nstielau/digirdu-lights/tests/test_sound_review.py

"""Tests for offline review through the producer audio pipeline."""

import array
import hashlib
import json
import math
import os
from pathlib import Path
import subprocess
import sys
import tempfile
import unittest
from unittest.mock import patch
import wave

from audio_features import Analyzer, AudioFeatures
from audio_events import DroneEventConfig
from animation import CulvertAnimation
from config import Config
from effects import FEATHERWING_PORTRAIT
from tools import sound_review
from tools.sound_review import (
    analyze_wav,
    build_artifacts,
    compare_drone,
    compare_labels,
    load_labels,
    portrait_pixels,
    read_wav_hops,
    render_effects,
    serialize_features,
)
from tools.record_fixture import validate_wav as validate_fixture_wav


FIXTURE_DIR = Path(__file__).parent.parent / "review" / "recordings"
REVIEW_AUDIO_FIXTURE = FIXTURE_DIR / "drone-yell-10s.wav"
REVIEW_LABEL_FIXTURE = FIXTURE_DIR / "drone-yell-10s.labels.json"
HIGH_YELL_AUDIO_FIXTURE = FIXTURE_DIR / "high-yell-01.wav"
HIGH_YELL_LABEL_FIXTURE = FIXTURE_DIR / "high-yell-01.labels.json"
REVIEW_AUDIO_SHA256 = "efa8b234ee94c014437b7d48fd6f612cd8aed68bb49764d009c5cb97f7cfafa2"


def write_pcm_wav(path, sample_rate_hz, samples):
    path = Path(path)
    little_endian = array.array("h", samples)
    if sys.byteorder != "little":
        little_endian.byteswap()
    with wave.open(str(path), "wb") as destination:
        destination.setnchannels(1)
        destination.setsampwidth(2)
        destination.setframerate(sample_rate_hz)
        destination.writeframes(little_endian.tobytes())
    return path


def fixture_feature_frames():
    """Small serialized feature timeline for deterministic renderer tests."""
    frames = []
    for time_ms in range(0, 1001, 100):
        level = 0.2 if time_ms < 500 else 0.8
        frames.append(
            {
                "time_ms": time_ms,
                "calibrating": False,
                "volume": level,
                "drone": level,
                "harmonics": 0.35,
                "timbre_position": 0.25,
                "growl": 0.15,
                "vocal": 0.1,
                "transient_strength": 0.0,
                "attack_event": False,
                "yell_event": False,
                "attack_age_s": 0.0,
                "yell_age_s": 0.0,
                "decay": level,
                "low_energy": 0.55,
                "mid_energy": 0.3,
                "high_energy": 0.15,
                "spectrum": (level, 0.5, 0.25, 0.1, 0.05, 0.0, 0.0, 0.0),
                "active": level > 0.0,
                "raw_rms": 100.0,
                "dominant_frequency_hz": 93.75,
            }
        )
    return frames


class CommittedSoundReviewFixtureTests(unittest.TestCase):
    def test_committed_fixture_is_reviewed_and_deterministic(self):
        self.assertEqual(
            hashlib.sha256(REVIEW_AUDIO_FIXTURE.read_bytes()).hexdigest(),
            REVIEW_AUDIO_SHA256,
        )
        self.assertEqual(
            validate_fixture_wav(REVIEW_AUDIO_FIXTURE),
            {
                "sample_rate_hz": 16000,
                "channels": 1,
                "sample_width_bytes": 2,
                "frame_count": 160000,
                "duration_s": 10.0,
            },
        )
        expected_labels = {
            "audio_file": REVIEW_AUDIO_FIXTURE.name,
            "sample_rate_hz": 16000,
            "labels": [
                {"type": "drone", "start_ms": 2250, "end_ms": 10000},
                {"type": "yell", "start_ms": 4250, "end_ms": 4750},
            ],
        }
        self.assertEqual(json.loads(REVIEW_LABEL_FIXTURE.read_text()), expected_labels)
        label_bytes = REVIEW_LABEL_FIXTURE.read_bytes()

        with tempfile.TemporaryDirectory() as temporary:
            temporary = Path(temporary)
            first = build_artifacts(
                REVIEW_AUDIO_FIXTURE, REVIEW_LABEL_FIXTURE, temporary / "first"
            )
            second = build_artifacts(
                REVIEW_AUDIO_FIXTURE, REVIEW_LABEL_FIXTURE, temporary / "second"
            )

            self.assertEqual(REVIEW_LABEL_FIXTURE.read_bytes(), label_bytes)
            first_events = json.loads(Path(first["events_json"]).read_text())
            event_times = [event["time_ms"] for event in first_events]
            self.assertEqual(event_times, sorted(event_times))
            self.assertTrue(all(0 <= time_ms <= 10000 for time_ms in event_times))
            for name in first:
                self.assertEqual(
                    Path(first[name]).read_bytes(),
                    Path(second[name]).read_bytes(),
                    name,
                )

    def test_high_yell_recording_has_authoritative_human_labels(self):
        self.assertEqual(
            validate_fixture_wav(HIGH_YELL_AUDIO_FIXTURE),
            {
                "sample_rate_hz": 16000,
                "channels": 1,
                "sample_width_bytes": 2,
                "frame_count": 160000,
                "duration_s": 10.0,
            },
        )
        self.assertEqual(
            json.loads(HIGH_YELL_LABEL_FIXTURE.read_text()),
            {
                "audio_file": "high-yell-01.wav",
                "sample_rate_hz": 16000,
                "labels": [
                    {"type": "drone", "start_ms": 1020, "end_ms": 6950},
                    {"type": "yell", "start_ms": 2950, "end_ms": 3050},
                ],
            },
        )


class SoundReviewWavTests(unittest.TestCase):
    def setUp(self):
        self.temporary = tempfile.TemporaryDirectory()
        self.addCleanup(self.temporary.cleanup)
        self.tempdir = Path(self.temporary.name)

    def test_read_wav_hops_uses_complete_1024_sample_frames(self):
        path = write_pcm_wav(
            self.tempdir / "take.wav", 16000, array.array("h", range(2048))
        )

        info, hops = read_wav_hops(path, Config())

        self.assertEqual(info["sample_rate_hz"], 16000)
        self.assertEqual([len(hop) for hop in hops], [1024, 1024])
        self.assertEqual(hops[0], array.array("h", range(1024)))
        self.assertEqual(hops[1], array.array("h", range(1024, 2048)))

    def test_exact_10_second_wav_pads_only_final_analysis_hop_and_builds_review(self):
        config = Config()
        sample_count = 10 * config.sample_rate
        samples = array.array("h", [0]) * sample_count
        samples[-256:] = array.array("h", range(1, 257))
        path = write_pcm_wav(self.tempdir / "take.wav", config.sample_rate, samples)
        labels_path = self.tempdir / "take.labels.json"
        labels_path.write_text(
            json.dumps(
                {
                    "audio_file": path.name,
                    "sample_rate_hz": config.sample_rate,
                    "labels": [],
                }
            )
        )

        info, hops = read_wav_hops(path, config)

        self.assertEqual(info["frame_count"], 160000)
        self.assertEqual(info["duration_ms"], 10000)
        self.assertEqual(len(hops), 157)
        self.assertEqual(len(hops[-1]), config.hop_size)
        self.assertEqual(hops[-1][:256], array.array("h", range(1, 257)))
        self.assertEqual(hops[-1][256:], array.array("h", [0]) * 768)

        seen_dts = []
        original_update = Analyzer.update

        def record_update(analyzer, raw, dt_s):
            seen_dts.append(dt_s)
            return original_update(analyzer, raw, dt_s)

        with patch.object(Analyzer, "update", record_update):
            artifacts = build_artifacts(
                path, labels_path, self.tempdir / "artifacts", config
            )
        result = json.loads(Path(artifacts["run_json"]).read_text())
        features = json.loads(Path(artifacts["features_json"]).read_text())
        bundle = json.loads(Path(artifacts["review_json"]).read_text())

        self.assertEqual(result["duration_ms"], 10000)
        self.assertEqual(len(seen_dts), 157)
        self.assertEqual(seen_dts[0], config.hop_size / config.sample_rate)
        self.assertEqual(seen_dts[-1], 0.016)
        self.assertEqual(features[-1]["time_ms"], 10000)
        self.assertNotIn(10048, [frame["time_ms"] for frame in features])
        self.assertEqual(bundle["duration_ms"], 10000)
        self.assertEqual(bundle["audio_url"], "../take.wav")
        self.assertEqual(bundle["features"], features)

    def test_read_wav_hops_rejects_invalid_wav_format(self):
        path = write_pcm_wav(
            self.tempdir / "take.wav", 8000, array.array("h", range(1024))
        )

        with self.assertRaises(ValueError):
            read_wav_hops(path, Config())

    def test_read_wav_hops_rejects_file_replacement_during_validation(self):
        path = write_pcm_wav(
            self.tempdir / "take.wav", 16000, array.array("h", range(2048))
        )
        replacement = write_pcm_wav(
            self.tempdir / "replacement.wav",
            16000,
            array.array("h", [42]) * 2048,
        )

        def validate_then_replace(*args, **kwargs):
            metadata = validate_fixture_wav(*args, **kwargs)
            os.replace(replacement, path)
            return metadata

        with patch(
            "tools.sound_review.validate_wav", side_effect=validate_then_replace
        ):
            with self.assertRaisesRegex(ValueError, "changed during validation"):
                read_wav_hops(path, Config())

    def test_read_wav_hops_rejects_metadata_changes_during_validation(self):
        path = write_pcm_wav(
            self.tempdir / "take.wav", 16000, array.array("h", range(2048))
        )

        def validate_with_stale_metadata(*args, **kwargs):
            metadata = dict(validate_fixture_wav(*args, **kwargs))
            metadata["frame_count"] = 1024
            return metadata

        with patch(
            "tools.sound_review.validate_wav",
            side_effect=validate_with_stale_metadata,
        ):
            with self.assertRaisesRegex(ValueError, "metadata changed"):
                read_wav_hops(path, Config())

    def test_load_labels_rejects_invalid_range_and_wrong_rate(self):
        path = self.tempdir / "labels.json"
        path.write_text(
            json.dumps(
                {
                    "audio_file": "take.wav",
                    "sample_rate_hz": 8000,
                    "labels": [
                        {"type": "drone", "start_ms": 900, "end_ms": 100}
                    ],
                }
            )
        )

        with self.assertRaises(ValueError):
            load_labels(path, duration_ms=1000, sample_rate_hz=16000)

    def test_load_labels_rejects_invalid_types_and_timestamps(self):
        invalid_labels = (
            {"type": "unknown", "start_ms": 100, "end_ms": 200},
            {"type": [], "start_ms": 100, "end_ms": 200},
            {"type": "drone", "start_ms": 100.5, "end_ms": 200},
            {"type": "drone", "start_ms": True, "end_ms": 200},
            {"type": "drone", "start_ms": -1, "end_ms": 200},
            {"type": "drone", "start_ms": 200, "end_ms": 100},
            {"type": "drone", "start_ms": 100, "end_ms": 1001},
        )
        for label in invalid_labels:
            with self.subTest(label=label):
                path = self.tempdir / "labels.json"
                path.write_text(
                    json.dumps(
                        {
                            "audio_file": "take.wav",
                            "sample_rate_hz": 16000,
                            "labels": [label],
                        }
                    )
                )
                with self.assertRaises(ValueError):
                    load_labels(path, duration_ms=1000, sample_rate_hz=16000)

    def test_load_labels_enforces_range_and_point_grammar(self):
        invalid_labels = (
            {"type": "drone", "start_ms": 100},
            {"type": "yell", "start_ms": 100, "end_ms": 100},
            {"type": "beat", "start_ms": 100, "end_ms": 101},
            {"type": "transient", "start_ms": 100, "end_ms": 200},
        )
        for index, label in enumerate(invalid_labels):
            with self.subTest(label=label):
                path = self.tempdir / f"invalid-grammar-{index}.json"
                path.write_text(
                    json.dumps(
                        {
                            "audio_file": "take.wav",
                            "sample_rate_hz": 16000,
                            "labels": [label],
                        }
                    )
                )
                with self.assertRaises(ValueError):
                    load_labels(path, duration_ms=1000, sample_rate_hz=16000)

        path = self.tempdir / "valid-points.json"
        path.write_text(
            json.dumps(
                {
                    "audio_file": "take.wav",
                    "sample_rate_hz": 16000,
                    "labels": [
                        {"type": "beat", "start_ms": 100},
                        {"type": "transient", "start_ms": 200, "end_ms": 200},
                    ],
                }
            )
        )
        self.assertEqual(
            load_labels(path, duration_ms=1000, sample_rate_hz=16000)["labels"],
            [
                {"type": "beat", "start_ms": 100, "end_ms": 100},
                {"type": "transient", "start_ms": 200, "end_ms": 200},
            ],
        )

    def test_load_labels_accepts_growl_range(self):
        path = self.tempdir / "growl-labels.json"
        path.write_text(
            json.dumps(
                {
                    "audio_file": "take.wav",
                    "sample_rate_hz": 16000,
                    "labels": [
                        {"type": "growl", "start_ms": 2500, "end_ms": 4500}
                    ],
                }
            )
        )
        self.assertEqual(
            load_labels(path, duration_ms=10000, sample_rate_hz=16000)["labels"],
            [{"type": "growl", "start_ms": 2500, "end_ms": 4500}],
        )

    def test_load_labels_rejects_invalid_document_shapes(self):
        invalid_documents = (
            [],
            {"sample_rate_hz": 16000, "labels": []},
            {"audio_file": "", "sample_rate_hz": 16000, "labels": []},
            {"audio_file": "take.wav", "sample_rate_hz": True, "labels": []},
            {"audio_file": "take.wav", "sample_rate_hz": 16000, "labels": {}},
            {
                "audio_file": "take.wav",
                "sample_rate_hz": 16000,
                "labels": ["drone"],
            },
        )
        for index, document in enumerate(invalid_documents):
            with self.subTest(document=document):
                path = self.tempdir / f"labels-{index}.json"
                path.write_text(json.dumps(document))
                with self.assertRaises(ValueError):
                    load_labels(path, duration_ms=1000, sample_rate_hz=16000)

    def test_load_labels_rejects_duplicate_metadata(self):
        path = self.tempdir / "labels.json"
        path.write_text(
            '{"audio_file":"first.wav","audio_file":"second.wav",'
            '"sample_rate_hz":16000,"labels":[]}'
        )

        with self.assertRaises(ValueError):
            load_labels(path, duration_ms=1000, sample_rate_hz=16000)


class SoundReviewAnalysisTests(unittest.TestCase):
    def setUp(self):
        self.temporary = tempfile.TemporaryDirectory()
        self.addCleanup(self.temporary.cleanup)
        self.tempdir = Path(self.temporary.name)

    def test_spectrogram_preview_maps_silence_to_fixed_floor(self):
        config = Config()
        hops = [array.array("h", [0]) * config.hop_size for _ in range(2)]

        self.assertTrue(hasattr(sound_review, "spectrogram_preview"))
        preview = sound_review.spectrogram_preview(hops, config)

        self.assertEqual(preview["min_frequency_hz"], 31.25)
        self.assertEqual(preview["max_frequency_hz"], 8000.0)
        self.assertEqual(preview["min_dbfs"], -90.0)
        self.assertEqual(preview["max_dbfs"], 0.0)
        self.assertEqual(preview["rows"], 64)
        self.assertEqual(preview["columns"], 2)
        self.assertEqual(preview["frames"], [[0] * 64, [0] * 64])

    def test_spectrogram_preview_places_tone_in_expected_log_band(self):
        config = Config()
        frequency_hz = 500.0
        samples = array.array(
            "h",
            (
                round(
                    12000
                    * math.sin(
                        2
                        * math.pi
                        * frequency_hz
                        * index
                        / config.sample_rate
                    )
                )
                for index in range(config.hop_size)
            ),
        )

        self.assertTrue(hasattr(sound_review, "spectrogram_preview"))
        first = sound_review.spectrogram_preview([samples], config)
        second = sound_review.spectrogram_preview([samples], config)
        peak_row = max(
            range(first["rows"]), key=first["frames"][0].__getitem__
        )
        expected_row = math.floor(
            math.log(frequency_hz / first["min_frequency_hz"])
            / math.log(
                first["max_frequency_hz"] / first["min_frequency_hz"]
            )
            * first["rows"]
        )

        self.assertEqual(first, second)
        self.assertLessEqual(abs(peak_row - expected_row), 1)
        self.assertGreater(first["frames"][0][peak_row], 0)
        self.assertTrue(
            all(0 <= value <= 255 for value in first["frames"][0])
        )

    def test_analyze_wav_uses_ordered_hop_end_timestamps_and_events(self):
        config = Config()
        frame_count = 10 * config.sample_rate // config.hop_size * config.hop_size
        samples = array.array("h")
        for index in range(frame_count):
            time_s = index / config.sample_rate
            value = 0.0
            if time_s >= 2.0:
                value += 3500 * math.sin(2 * math.pi * 93.75 * time_s)
            if 4.8 <= time_s < 5.2:
                value += 7000 * math.sin(2 * math.pi * 2500 * time_s)
            samples.append(round(value))
        audio_path = write_pcm_wav(
            self.tempdir / "take.wav", config.sample_rate, samples
        )
        duration_ms = round(frame_count * 1000 / config.sample_rate)
        labels_path = self.tempdir / "labels.json"
        labels_path.write_text(
            json.dumps(
                {
                    "audio_file": audio_path.name,
                    "sample_rate_hz": config.sample_rate,
                    "labels": [
                        {"type": "drone", "start_ms": 2000, "end_ms": duration_ms},
                        {"type": "yell", "start_ms": 4800, "end_ms": 5200},
                    ],
                }
            )
        )

        result = analyze_wav(audio_path, labels_path, config, fps=20)

        self.assertEqual(
            [frame["time_ms"] for frame in result["features"]],
            [
                round(index * config.hop_size * 1000 / config.sample_rate)
                for index in range(1, frame_count // config.hop_size + 1)
            ],
        )
        self.assertIn(
            result["events"][0]["type"], {"drone_start", "transient", "yell"}
        )
        self.assertEqual(result["fps"], 20)

    def test_analyze_wav_uses_exact_sample_end_delta_for_1025_samples(self):
        config = Config()
        audio_path = write_pcm_wav(
            self.tempdir / "unaligned.wav",
            config.sample_rate,
            array.array("h", [0]) * 1025,
        )
        labels_path = self.tempdir / "labels.json"
        labels_path.write_text(
            json.dumps(
                {
                    "audio_file": audio_path.name,
                    "sample_rate_hz": config.sample_rate,
                    "labels": [],
                }
            )
        )
        seen_dts = []
        original_update = Analyzer.update

        def record_update(analyzer, raw, dt_s):
            seen_dts.append(dt_s)
            return original_update(analyzer, raw, dt_s)

        with patch.object(Analyzer, "update", record_update):
            result = analyze_wav(audio_path, labels_path, config)

        timestamps = [frame["time_ms"] for frame in result["features"]]
        self.assertEqual(result["info"]["duration_ms"], 65)
        self.assertEqual(timestamps, [64, 65])
        self.assertEqual(seen_dts, [1024 / config.sample_rate, 1 / config.sample_rate])
        self.assertEqual(timestamps, sorted(set(timestamps)))

    def test_analyze_wav_uses_actual_duration_for_shorter_than_hop_audio(self):
        config = Config()
        audio_path = write_pcm_wav(
            self.tempdir / "short.wav",
            config.sample_rate,
            array.array("h", [0]) * 512,
        )
        labels_path = self.tempdir / "labels.json"
        labels_path.write_text(
            json.dumps(
                {
                    "audio_file": audio_path.name,
                    "sample_rate_hz": config.sample_rate,
                    "labels": [],
                }
            )
        )
        seen_dts = []
        original_update = Analyzer.update

        def record_update(analyzer, raw, dt_s):
            seen_dts.append(dt_s)
            return original_update(analyzer, raw, dt_s)

        with patch.object(Analyzer, "update", record_update):
            result = analyze_wav(audio_path, labels_path, config)

        self.assertEqual(result["info"]["duration_ms"], 32)
        self.assertEqual([frame["time_ms"] for frame in result["features"]], [32])
        self.assertEqual(seen_dts, [512 / config.sample_rate])

    def test_analyze_wav_rejects_labels_for_a_different_audio_file(self):
        config = Config()
        audio_path = write_pcm_wav(
            self.tempdir / "take.wav",
            config.sample_rate,
            array.array("h", [0]) * config.hop_size,
        )
        labels_path = self.tempdir / "labels.json"
        labels_path.write_text(
            json.dumps(
                {
                    "audio_file": "other.wav",
                    "sample_rate_hz": config.sample_rate,
                    "labels": [],
                }
            )
        )

        with self.assertRaises(ValueError):
            analyze_wav(audio_path, labels_path, config)

    def test_analyze_wav_rejects_invalid_fps(self):
        config = Config()
        audio_path = write_pcm_wav(
            self.tempdir / "take.wav",
            config.sample_rate,
            array.array("h", [0]) * config.hop_size,
        )
        labels_path = self.tempdir / "labels.json"
        labels_path.write_text(
            json.dumps(
                {
                    "audio_file": audio_path.name,
                    "sample_rate_hz": config.sample_rate,
                    "labels": [],
                }
            )
        )

        for fps in (True, 0, -1, math.nan, math.inf, -math.inf):
            with self.subTest(fps=fps):
                with self.assertRaises(ValueError):
                    analyze_wav(audio_path, labels_path, config, fps=fps)

    def test_serialize_features_is_normalized_finite_and_non_mutating(self):
        current = AudioFeatures()
        current.volume = 0.4
        current.drone = 0.5
        current.harmonics = 0.35
        current.timbrePosition = 0.25
        current.growl = 0.6
        current.vocal = 0.7
        current.attack = 0.8
        current.attackEvent = True
        current.yellEvent = False
        current.attackAge = 0.02
        current.yellAge = 0.0
        current.decay = 0.9
        current.spectrum = tuple(index / 10 for index in range(8))
        before = dict(vars(current))
        raw = {
            "rms": 123.0,
            "drone_hz": 93.75,
            "bands": (5.0, 3.0, 1.0, 0.5, 0.5),
        }

        serialized = serialize_features(current, raw, 64)

        self.assertEqual(vars(current), before)
        self.assertEqual(
            set(serialized),
            {
                "time_ms",
                "calibrating",
                "volume",
                "drone",
                "harmonics",
                "timbre_position",
                "growl",
                "vocal",
                "transient_strength",
                "attack_event",
                "yell_event",
                "attack_age_s",
                "yell_age_s",
                "decay",
                "low_energy",
                "mid_energy",
                "high_energy",
                "spectrum",
                "active",
                "raw_rms",
                "dominant_frequency_hz",
            },
        )
        for name in (
            "volume",
            "drone",
            "growl",
            "vocal",
            "transient_strength",
            "low_energy",
            "mid_energy",
            "high_energy",
        ):
            self.assertGreaterEqual(serialized[name], 0.0)
            self.assertLessEqual(serialized[name], 1.0)
        self.assertEqual(serialized["low_energy"], 0.5)
        self.assertEqual(serialized["mid_energy"], 0.4)
        self.assertEqual(serialized["high_energy"], 0.1)
        self.assertEqual(serialized["harmonics"], 0.35)
        self.assertEqual(serialized["timbre_position"], 0.25)
        self.assertTrue(serialized["attack_event"])
        self.assertFalse(serialized["yell_event"])
        self.assertEqual(serialized["attack_age_s"], 0.02)
        self.assertEqual(serialized["yell_age_s"], 0.0)
        self.assertEqual(serialized["decay"], 0.9)
        self.assertEqual(
            serialized["spectrum"], tuple(index / 10 for index in range(8))
        )

    def test_serialize_features_rejects_non_finite_values(self):
        current = AudioFeatures()
        raw = {
            "rms": math.inf,
            "drone_hz": 93.75,
            "bands": (0.0, 0.0, 0.0, 0.0, 0.0),
        }

        with self.assertRaises(ValueError):
            serialize_features(current, raw, 64)


class SoundReviewMetricTests(unittest.TestCase):
    def setUp(self):
        self.temporary = tempfile.TemporaryDirectory()
        self.addCleanup(self.temporary.cleanup)
        self.tempdir = Path(self.temporary.name)

    def test_compare_events_reports_one_match_one_false_positive_and_one_miss(self):
        labels = [
            {"type": "yell", "start_ms": 1000, "end_ms": 1200},
            {"type": "yell", "start_ms": 3000, "end_ms": 3200},
        ]
        detected = [
            {"type": "yell", "time_ms": 1100, "confidence": 0.9},
            {"type": "yell", "time_ms": 5000, "confidence": 0.7},
        ]

        report = compare_labels(labels, detected, tolerance_ms=250)

        self.assertEqual(report["yell"]["true_positive"], 1)
        self.assertEqual(report["yell"]["false_positive"], 1)
        self.assertEqual(report["yell"]["false_negative"], 1)
        self.assertAlmostEqual(report["yell"]["precision"], 0.5)
        self.assertAlmostEqual(report["yell"]["recall"], 0.5)
        self.assertAlmostEqual(report["yell"]["f1"], 0.5)
        self.assertEqual(report["yell"]["timing_error_ms"], [100])
        self.assertEqual(report["yell"]["absolute_timing_error_ms"], [100])

    def test_compare_labels_matches_each_detection_only_once(self):
        labels = [
            {"type": "beat", "start_ms": 1000, "end_ms": 1000},
            {"type": "beat", "start_ms": 2000, "end_ms": 2000},
        ]
        detected = [
            {"type": "beat", "time_ms": 1050},
            {"type": "beat", "time_ms": 2050},
            {"type": "beat", "time_ms": 2100},
        ]

        report = compare_labels(labels, detected, tolerance_ms=100)

        self.assertEqual(report["beat"]["true_positive"], 2)
        self.assertEqual(report["beat"]["false_positive"], 1)
        self.assertEqual(report["beat"]["false_negative"], 0)
        self.assertEqual(report["beat"]["unmatched_labels"], [])
        self.assertEqual(report["beat"]["unmatched_events"], [{"type": "beat", "time_ms": 2100}])

    def test_compare_labels_maximizes_matches_for_overlapping_ranges(self):
        labels = [
            {"type": "yell", "start_ms": 1000, "end_ms": 3000},
            {"type": "yell", "start_ms": 2000, "end_ms": 2050},
        ]
        detected = [
            {"type": "yell", "time_ms": 1800},
            {"type": "yell", "time_ms": 2500},
        ]

        report = compare_labels(labels, detected, tolerance_ms=250)

        self.assertEqual(report["yell"]["true_positive"], 2)
        self.assertEqual(report["yell"]["false_positive"], 0)
        self.assertEqual(report["yell"]["false_negative"], 0)
        self.assertEqual(report["yell"]["timing_error_ms"], [1500, -200])

    def test_compare_drone_reports_bounds_and_time_errors(self):
        report = compare_drone(
            {"start_ms": 2000, "end_ms": 8000},
            [
                {"type": "drone_start", "time_ms": 2200},
                {"type": "drone_stop", "time_ms": 7600},
            ],
            duration_ms=10000,
        )

        self.assertEqual(report["start_error_ms"], 200)
        self.assertEqual(report["stop_error_ms"], -400)
        self.assertAlmostEqual(report["intersection_over_union"], 5400 / 6000)
        self.assertEqual(report["false_active_ms"], 0)
        self.assertEqual(report["false_inactive_ms"], 600)

    def test_compare_drone_scores_disjoint_detected_spans_as_a_union(self):
        report = compare_drone(
            {"start_ms": 2000, "end_ms": 8000},
            [
                {"type": "drone_start", "time_ms": 1000},
                {"type": "drone_stop", "time_ms": 3000},
                {"type": "drone_start", "time_ms": 5000},
                {"type": "drone_stop", "time_ms": 6000},
            ],
            duration_ms=10000,
        )

        self.assertEqual(report["start_error_ms"], -1000)
        self.assertEqual(report["stop_error_ms"], -2000)
        self.assertAlmostEqual(report["intersection_over_union"], 2 / 7)
        self.assertEqual(report["false_active_ms"], 1000)
        self.assertEqual(report["false_inactive_ms"], 4000)

    def test_compare_drone_accepts_repeated_human_spans_without_changing_report_shape(self):
        report = compare_drone(
            [
                {"start_ms": 1000, "end_ms": 2000},
                {"start_ms": 4000, "end_ms": 5000},
            ],
            [
                {"type": "drone_start", "time_ms": 1000},
                {"type": "drone_stop", "time_ms": 2000},
                {"type": "drone_start", "time_ms": 4000},
                {"type": "drone_stop", "time_ms": 5000},
            ],
            duration_ms=10000,
        )

        self.assertEqual(
            set(report),
            {
                "start_error_ms",
                "stop_error_ms",
                "intersection_over_union",
                "false_active_ms",
                "false_inactive_ms",
            },
        )
        self.assertEqual(report["intersection_over_union"], 1.0)
        self.assertEqual(report["false_active_ms"], 0)
        self.assertEqual(report["false_inactive_ms"], 0)

    def test_compare_drone_reports_missing_bounds_without_dividing_by_zero(self):
        label = {"start_ms": 2000, "end_ms": 8000}

        for events, expected_start, expected_stop in (
            ([], None, None),
            ([{"type": "drone_start", "time_ms": 2200}], 200, None),
            ([{"type": "drone_stop", "time_ms": 7600}], None, -400),
        ):
            with self.subTest(events=events):
                report = compare_drone(label, events, duration_ms=10000)
                self.assertEqual(report["start_error_ms"], expected_start)
                self.assertEqual(report["stop_error_ms"], expected_stop)
                self.assertEqual(report["intersection_over_union"], 0.0)
                self.assertEqual(report["false_active_ms"], 0)
                self.assertEqual(report["false_inactive_ms"], 6000)

    def test_compare_drone_rejects_zero_length_and_out_of_range_labels(self):
        invalid_labels = (
            {"start_ms": 2000, "end_ms": 2000},
            {"start_ms": 8000, "end_ms": 7000},
            {"start_ms": 0, "end_ms": 10001},
        )
        for label in invalid_labels:
            with self.subTest(label=label):
                with self.assertRaises(ValueError):
                    compare_drone(label, [], duration_ms=10000)

        with self.assertRaises(ValueError):
            compare_drone(
                {"start_ms": 1000, "end_ms": 2000},
                [
                    {"type": "drone_start", "time_ms": 1500},
                    {"type": "drone_stop", "time_ms": 1500},
                ],
                duration_ms=10000,
            )

    def test_metrics_reject_extreme_finite_values_before_arithmetic(self):
        with self.assertRaises(ValueError):
            compare_drone(
                {"start_ms": 0, "end_ms": 1e308}, [], duration_ms=1e308
            )
        with self.assertRaises(ValueError):
            compare_labels(
                [{"type": "beat", "start_ms": 0, "end_ms": 0}],
                [],
                tolerance_ms=1e308,
            )

    def test_analyze_wav_adds_comparison_without_mutating_labels(self):
        config = Config()
        audio_path = write_pcm_wav(
            self.tempdir / "take.wav",
            config.sample_rate,
            array.array("h", [0]) * config.hop_size,
        )
        labels_path = audio_path.with_suffix(".labels.json")
        original = {
            "audio_file": audio_path.name,
            "sample_rate_hz": config.sample_rate,
            "labels": [],
        }
        labels_path.write_text(json.dumps(original))

        result = analyze_wav(audio_path, labels_path, config)

        self.assertIn("comparison", result)
        self.assertEqual(result["labels"]["labels"], [])
        self.assertEqual(json.loads(labels_path.read_text()), original)


class SoundReviewEffectTests(unittest.TestCase):
    def setUp(self):
        self.temporary = tempfile.TemporaryDirectory()
        self.addCleanup(self.temporary.cleanup)
        self.tempdir = Path(self.temporary.name)

    def test_portrait_pixels_converts_grb_and_reorders_physical_pixels(self):
        grb = bytearray(96)
        for physical in range(32):
            offset = physical * 3
            grb[offset : offset + 3] = bytes(
                (physical, physical + 32, physical + 64)
            )

        pixels = portrait_pixels(grb)

        self.assertEqual(len(pixels), 32)
        for logical, physical in enumerate(FEATHERWING_PORTRAIT):
            self.assertEqual(
                pixels[logical],
                [physical + 32, physical, physical + 64],
            )

    def test_render_effects_serializes_portrait_frames_for_three_nodes(self):
        effects = render_effects(
            fixture_feature_frames(),
            Config(),
            fps=20,
            node_distances_mm=(-5000, 0, 5000),
            virtual_wave_speed_mm_s=10000,
        )

        self.assertEqual(effects["node_distances_mm"], [-5000, 0, 5000])
        self.assertEqual(
            set(effects["effects"]),
            {"Spectrum", "Ember", "Aurora", "Ripple", "Chroma"},
        )
        self.assertEqual(effects["pixel_count"], 32)
        self.assertEqual(
            effects["pixel_layout"],
            {"columns": 4, "rows": 8, "order": "row-major-portrait"},
        )
        self.assertEqual(
            len(effects["frames"]["Spectrum"]["0"][0]["pixels_rgb"]), 32
        )
        self.assertTrue(
            all(
                len(pixel) == 3
                for pixel in effects["frames"]["Spectrum"]["0"][0][
                    "pixels_rgb"
                ]
            )
        )

    def test_render_effects_uses_absolute_causal_delay_for_nodes(self):
        effects = render_effects(
            fixture_feature_frames(),
            Config(),
            fps=2,
            node_distances_mm=(-5000, 0, 5000),
            virtual_wave_speed_mm_s=10000,
        )

        midpoint = effects["frames"]["Spectrum"]["1"][1]
        outward = effects["frames"]["Spectrum"]["0"][1]
        opposite = effects["frames"]["Spectrum"]["2"][1]
        self.assertEqual(midpoint["time_ms"], 500)
        self.assertEqual(midpoint["source_time_ms"], 500)
        self.assertEqual(outward["source_time_ms"], 0)
        self.assertEqual(opposite["source_time_ms"], 0)

    def test_render_effects_keeps_delayed_node_neutral_before_causal_delay(self):
        frames = fixture_feature_frames()
        frames[0].update(
            attack_event=True,
            attack_age_s=0.0,
            transient_strength=1.0,
        )
        rendered = render_effects(
            frames,
            Config(),
            fps=2,
            node_distances_mm=(5000,),
            virtual_wave_speed_mm_s=10000,
        )["frames"]["Ember"]["0"]

        self.assertEqual(rendered[0]["time_ms"], 0)
        self.assertIsNone(rendered[0]["source_time_ms"])
        self.assertEqual(rendered[0]["pixels_rgb"], [[0, 0, 0]] * 32)
        self.assertEqual(rendered[1]["time_ms"], 500)
        self.assertEqual(rendered[1]["source_time_ms"], 0)
        self.assertNotEqual(rendered[1]["pixels_rgb"], [[0, 0, 0]] * 32)

    def test_render_effects_preserves_semantic_event_bloom_and_pulse(self):
        plain = fixture_feature_frames()
        with_event = fixture_feature_frames()
        with_event[5]["transient_strength"] = 1.0
        with_event[5]["attack_event"] = True
        with_event[5]["attack_age_s"] = 0.0

        plain_output = render_effects(
            plain, Config(), fps=20, node_distances_mm=(0,), virtual_wave_speed_mm_s=10000
        )
        event_output = render_effects(
            with_event,
            Config(),
            fps=20,
            node_distances_mm=(0,),
            virtual_wave_speed_mm_s=10000,
        )

        plain_frames = plain_output["frames"]["Ember"]["0"]
        event_frames = event_output["frames"]["Ember"]["0"]
        self.assertTrue(
            any(
                left["pixels_rgb"] != right["pixels_rgb"]
                for left, right in zip(plain_frames, event_frames)
            )
        )

    def test_render_effects_delivers_event_on_terminal_feature_frame(self):
        plain = fixture_feature_frames()
        with_event = fixture_feature_frames()
        with_event[-1]["transient_strength"] = 1.0
        with_event[-1]["attack_event"] = True
        with_event[-1]["attack_age_s"] = 0.0

        plain_frames = render_effects(
            plain, Config(), fps=20, node_distances_mm=(0,), virtual_wave_speed_mm_s=10000
        )["frames"]["Ember"]["0"]
        event_frames = render_effects(
            with_event,
            Config(),
            fps=20,
            node_distances_mm=(0,),
            virtual_wave_speed_mm_s=10000,
        )["frames"]["Ember"]["0"]

        self.assertEqual(event_frames[-1]["time_ms"], 1000)
        self.assertEqual(event_frames[-1]["source_time_ms"], 1000)
        self.assertNotEqual(plain_frames[-1]["pixels_rgb"], event_frames[-1]["pixels_rgb"])

    def test_render_effects_delivers_terminal_event_after_node_delay(self):
        plain = fixture_feature_frames()
        with_event = fixture_feature_frames()
        with_event[-1]["transient_strength"] = 1.0
        with_event[-1]["attack_event"] = True
        with_event[-1]["attack_age_s"] = 0.0
        render_kwargs = {
            "fps": 20,
            "node_distances_mm": (5000,),
            "virtual_wave_speed_mm_s": 10000,
        }

        plain_frames = render_effects(plain, Config(), **render_kwargs)["frames"]["Ember"]["0"]
        event_frames = render_effects(
            with_event, Config(), **render_kwargs
        )["frames"]["Ember"]["0"]

        self.assertEqual(event_frames[-1]["time_ms"], 1500)
        self.assertEqual(event_frames[-1]["source_time_ms"], 1000)
        self.assertNotEqual(plain_frames[-1]["pixels_rgb"], event_frames[-1]["pixels_rgb"])

    def test_render_effects_uses_actual_delta_for_fractional_delayed_tail(self):
        render_dts = []
        original_render = CulvertAnimation.render

        def capture_render(renderer, features, dt):
            render_dts.append(dt)
            return original_render(renderer, features, dt)

        with patch.object(CulvertAnimation, "render", capture_render):
            render_effects(
                fixture_feature_frames(),
                Config(),
                fps=20,
                node_distances_mm=(501,),
                virtual_wave_speed_mm_s=10000,
            )

        frames_per_effect = len(render_dts) // 5
        self.assertEqual(len(render_dts), frames_per_effect * 5)
        self.assertEqual(
            render_dts[frames_per_effect - 1 :: frames_per_effect], [0.001] * 5
        )

    def test_render_effects_drains_all_events_crossed_before_delayed_terminal_frame(self):
        frames = fixture_feature_frames()
        for frame in frames:
            if frame["time_ms"] in (800, 900, 1000):
                frame.update(
                    attack_event=True,
                    yell_event=True,
                    attack_age_s=0.0,
                    yell_age_s=0.0,
                    transient_strength=1.0,
                    vocal=1.0,
                )

        delivered = {"attack": 0, "yell": 0}
        original_render = CulvertAnimation.render

        def capture_render(renderer, features, dt):
            if features.attackEvent:
                delivered["attack"] += 1
            if features.yellEvent:
                delivered["yell"] += 1
            return original_render(renderer, features, dt)

        with patch.object(CulvertAnimation, "render", capture_render):
            render_effects(
                frames,
                Config(),
                fps=2,
                node_distances_mm=(5000,),
                virtual_wave_speed_mm_s=10000,
            )

        self.assertEqual(delivered, {"attack": 15, "yell": 15})

    def test_render_effects_rejects_fps_that_cannot_serialize_millisecond_timeline(self):
        with self.assertRaisesRegex(ValueError, "at most 1000"):
            render_effects(
                fixture_feature_frames(),
                Config(),
                fps=1001,
                node_distances_mm=(0,),
                virtual_wave_speed_mm_s=10000,
            )

    def test_render_effects_consumes_sample_held_event_only_once(self):
        coarse = fixture_feature_frames()
        for frame in coarse:
            frame.update(
                volume=0.0,
                drone=0.0,
                harmonics=0.0,
                timbre_position=0.0,
                growl=0.0,
                vocal=0.0,
                transient_strength=0.0,
                decay=0.0,
                spectrum=(0.0,) * 8,
                active=False,
            )
        coarse[5]["transient_strength"] = 0.8
        coarse[5]["attack_event"] = True
        fine = fixture_feature_frames()
        for frame in fine:
            frame.update(
                volume=0.0,
                drone=0.0,
                harmonics=0.0,
                timbre_position=0.0,
                growl=0.0,
                vocal=0.0,
                transient_strength=0.0,
                decay=0.0,
                spectrum=(0.0,) * 8,
                active=False,
            )
        fine[5]["transient_strength"] = 0.8
        fine[5]["attack_event"] = True
        event_frame = dict(fine[5])
        event_frame["time_ms"] = 501
        event_frame["attack_event"] = False
        event_frame["transient_strength"] = 0.0
        fine.insert(6, event_frame)

        coarse_output = render_effects(
            coarse,
            Config(),
            fps=20,
            node_distances_mm=(0,),
            virtual_wave_speed_mm_s=10000,
        )
        fine_output = render_effects(
            fine,
            Config(),
            fps=20,
            node_distances_mm=(0,),
            virtual_wave_speed_mm_s=10000,
        )

        coarse_frames = coarse_output["frames"]["Ember"]["0"]
        fine_frames = fine_output["frames"]["Ember"]["0"]
        for left, right in zip(coarse_frames, fine_frames):
            if left["time_ms"] >= 550:
                self.assertEqual(left["pixels_rgb"], right["pixels_rgb"])

    def test_artifacts_are_byte_stable_and_manifest_is_hashed_without_clock_data(
        self,
    ):
        config = Config()
        audio_path = write_pcm_wav(
            self.tempdir / "take.wav",
            config.sample_rate,
            array.array("h", [0]) * (config.hop_size * 3),
        )
        labels_path = self.tempdir / "take.labels.json"
        labels_path.write_text(
            json.dumps(
                {
                    "audio_file": audio_path.name,
                    "sample_rate_hz": config.sample_rate,
                    "labels": [],
                }
            )
        )
        output_dir = self.tempdir / "artifacts"
        detector_config = DroneEventConfig(
            on_threshold=0.71,
            off_threshold=0.19,
            start_hold_s=0.17,
            stop_hold_s=0.41,
        )

        first = build_artifacts(
            audio_path,
            labels_path,
            output_dir,
            config,
            detector_config=detector_config,
        )
        first_bytes = {
            name: Path(path).read_bytes()
            for name, path in first.items()
        }
        second = build_artifacts(
            audio_path,
            labels_path,
            output_dir,
            config,
            detector_config=detector_config,
        )
        second_bytes = {
            name: Path(path).read_bytes()
            for name, path in second.items()
        }

        self.assertEqual(first_bytes, second_bytes)
        manifest = json.loads(Path(first["run_json"]).read_text())
        self.assertEqual(manifest["random_seed"], 0)
        self.assertNotIn("generated_at", manifest)
        self.assertEqual(manifest["analysis"]["feature_fps"], 16000 / 1024)
        self.assertEqual(manifest["effect_engine"]["fps"], 20)
        self.assertEqual(
            manifest["analysis"]["detector"],
            {
                "drone_on_threshold": 0.71,
                "drone_off_threshold": 0.19,
                "drone_start_hold_s": 0.17,
                "drone_stop_hold_s": 0.41,
            },
        )
        self.assertEqual(
            set(manifest["source_sha256"]),
            {"audio", "labels"},
        )
        self.assertEqual(
            set(manifest["module_sha256"]),
            {
                "audio_spectrum.py",
                "audio_features.py",
                "audio_events.py",
                "animation.py",
                "effects.py",
                "config.py",
                "tools/sound_review.py",
            },
        )

    def test_artifacts_include_a_deterministic_browser_review_bundle(self):
        config = Config()
        audio_path = write_pcm_wav(
            self.tempdir / "take.wav",
            config.sample_rate,
            array.array("h", [0]) * (config.hop_size * 3),
        )
        labels_path = self.tempdir / "take.labels.json"
        labels_path.write_text(
            json.dumps(
                {
                    "audio_file": audio_path.name,
                    "sample_rate_hz": config.sample_rate,
                    "labels": [],
                }
            )
        )
        output_dir = self.tempdir / "artifacts"

        paths = build_artifacts(audio_path, labels_path, output_dir, config)

        self.assertIn("review_json", paths)
        bundle = json.loads(Path(paths["review_json"]).read_text())
        self.assertEqual(
            set(bundle),
            {
                "schema_version",
                "duration_ms",
                "sample_rate_hz",
                "audio_url",
                "waveform",
                "spectrogram",
                "labels",
                "features",
                "events",
                "effects",
                "comparison",
            },
        )
        self.assertEqual(bundle["schema_version"], 2)
        self.assertEqual(bundle["duration_ms"], 192)
        self.assertEqual(bundle["sample_rate_hz"], config.sample_rate)
        self.assertEqual(bundle["audio_url"], "../take.wav")
        self.assertEqual(
            bundle["spectrogram"]["columns"], len(bundle["waveform"])
        )
        self.assertEqual(bundle["spectrogram"]["rows"], 64)
        self.assertTrue(
            all(
                len(frame) == bundle["spectrogram"]["rows"]
                for frame in bundle["spectrogram"]["frames"]
            )
        )
        self.assertEqual(bundle["labels"], [])
        self.assertEqual(bundle["features"], json.loads(Path(paths["features_json"]).read_text()))
        self.assertEqual(bundle["events"], json.loads(Path(paths["events_json"]).read_text()))
        self.assertEqual(bundle["effects"], json.loads(Path(paths["effects_json"]).read_text()))
        self.assertEqual(
            bundle["comparison"],
            json.loads(Path(paths["run_json"]).read_text())["comparison"],
        )

    def test_sound_review_cli_is_executable_from_repository_root(self):
        root = Path(__file__).resolve().parent.parent
        completed = subprocess.run(
            [sys.executable, str(root / "tools/sound_review.py"), "--help"],
            cwd=root,
            capture_output=True,
            text=True,
            check=False,
        )
        self.assertEqual(completed.returncode, 0, completed.stderr)
        self.assertIn("--output-dir", completed.stdout)


if __name__ == "__main__":
    unittest.main()
